JakubNowek/EAGLE/project_counter/counter.sch

## EAGLE design project_counter/counter.sch (2022-02-19)

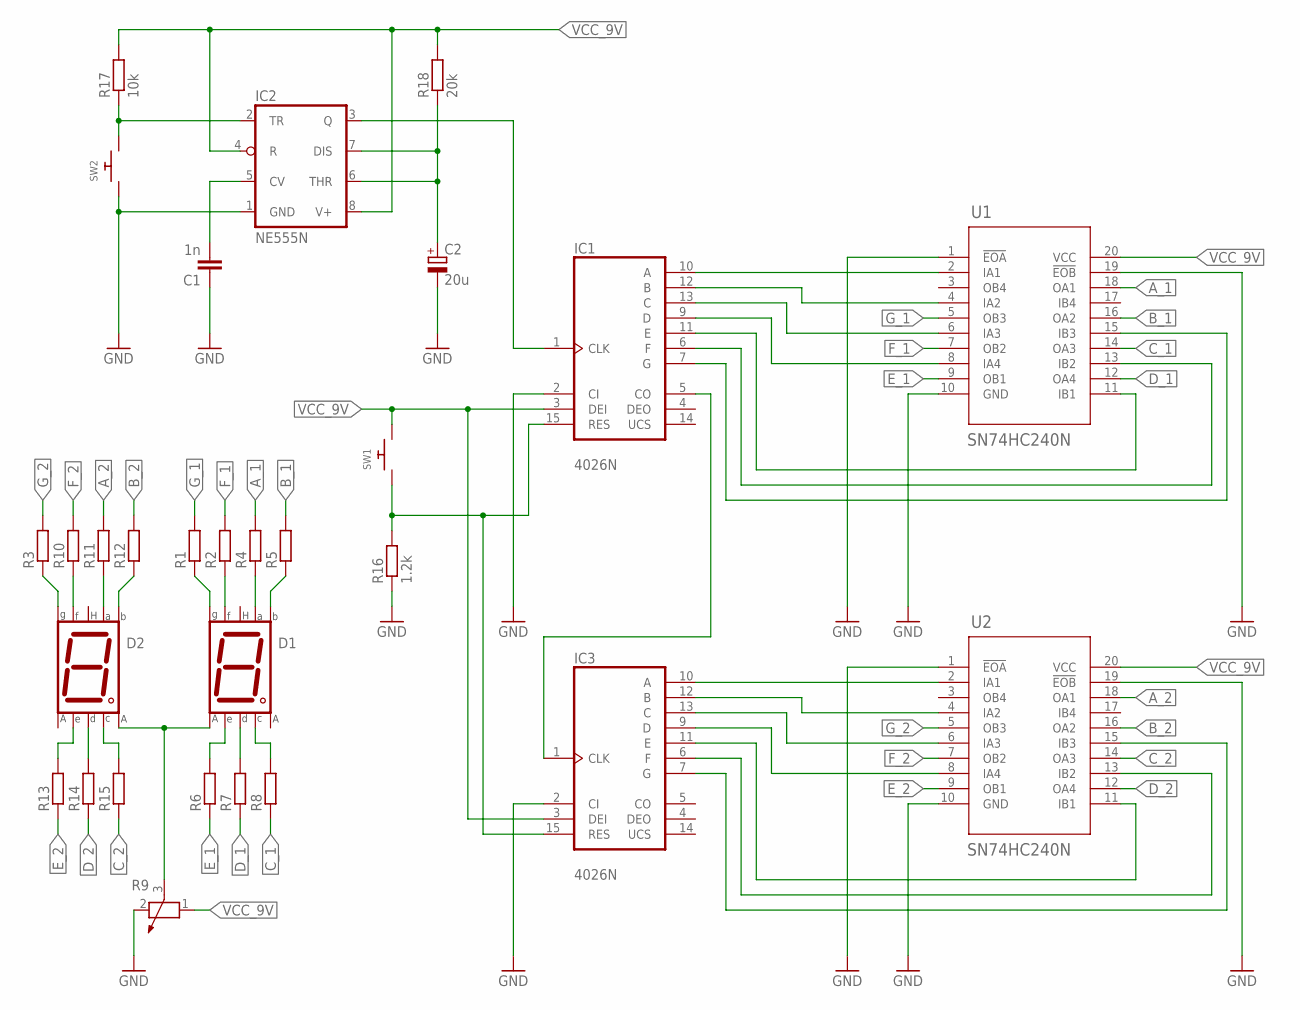
[picture p4: schematic counter.sch]

Parts:
C1: 1n; C025-024X044
C2: 20u; E5-5
D1, D2: 7SEG-CA; 7SEG-13
IC1, IC3: 4026N; DIL16
IC2: NE555N; DIL08-ROUND
R1, R2, R3, R4, R5, R6, R7, R8, R10, R11, R12, R13, R14, R15: R-EU_0204/5; 0204/5
R9: POTENTIOMETER_PT-10; PT-10
R16: 1.2k; 0204/5
R17: 10k; 0204/5
R18: 20k; 0204/5
SW1, SW2: SWITCH_PUSHBUTTONEVQ-PE; TACT_PANA-EVQ
U1, U2: SN74HC240N; N20

Connections:
A_1: U1.18 (OA1)
A_2: U2.18 (OA1)
B_1: U1.16 (OA2)
B_2: U2.16 (OA2)
C_1: U1.14 (OA3)
C_2: U2.14 (OA3)
D_1: U1.12 (OA4)
D_2: U2.12 (OA4)
E_1: U1.9 (OB1)
E_2: U2.9 (OB1)
F_1: U1.7 (OB2)
F_2: U2.7 (OB2)
GND: C1.1, C2.-, IC1.2 (CI), IC2.1 (GND), IC3.2 (CI), R9.2, R16.1, SW2.P$1, U1.1 (!EOA), U1.10 (GND), U1.19 (!EOB), U2.1 (!EOA), U2.10 (GND), U2.19 (!EOB)
G_1: U1.5 (OB3)
G_2: U2.5 (OB3)
unnamed: IC1.10 (A), U1.2 (IA1)
unnamed: IC1.12 (B), U1.4 (IA2)
unnamed: IC1.13 (C), U1.6 (IA3)
unnamed: IC1.9 (D), U1.8 (IA4)
unnamed: IC1.11 (E), U1.11 (IB1)
unnamed: IC1.6 (F), U1.13 (IB2)
unnamed: IC1.7 (G), U1.15 (IB3)
unnamed: D1.10 (G), R1.1
unnamed: D1.9 (F), R2.1
unnamed: D1.7 (A), R4.1
unnamed: D2.10 (G), R3.1
unnamed: D1.6 (B), R5.1
unnamed: D1.2 (D), R7.2
unnamed: D1.1 (E), R6.2
unnamed: D1.4 (C), R8.2
unnamed: D1.3 (CA1), D2.8 (CA2), R9.3
unnamed: D2.6 (B), R12.1
unnamed: D2.2 (D), R14.2
unnamed: D2.1 (E), R13.2
unnamed: D2.4 (C), R15.2
unnamed: IC1.3 (DEI), IC3.3 (DEI), SW1.P$2
unnamed: IC1.15 (RES), IC3.15 (RES), R16.2, SW1.P$1
unnamed: D2.9 (F), R10.1
unnamed: D2.7 (A), R11.1
unnamed: C2.+, IC2.6 (THR), IC2.7 (DIS), R18.1
unnamed: IC2.2 (TR), R17.1, SW2.P$2
unnamed: IC1.1 (CLK), IC2.3 (Q)
unnamed: IC3.10 (A), U2.2 (IA1)
unnamed: C1.2, IC2.5 (CV)
unnamed: IC1.5 (CO), IC3.1 (CLK)
unnamed: IC3.12 (B), U2.4 (IA2)
unnamed: IC3.13 (C), U2.6 (IA3)
unnamed: IC3.9 (D), U2.8 (IA4)
unnamed: IC3.11 (E), U2.11 (IB1)
unnamed: IC3.6 (F), U2.13 (IB2)
unnamed: IC3.7 (G), U2.15 (IB3)
VCC_9V: IC2.4 (R), IC2.8 (V+), R17.2, R18.2, U1.20 (VCC), U2.20 (VCC)
